pixelbreaker/buteo/buteo-mx/stls/trackpad-lower.stl

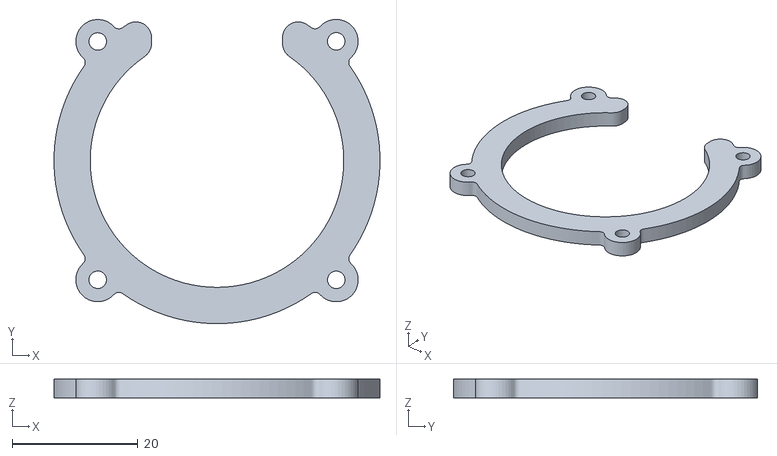
[picture p15: CAD file, 2024-01-28]
buteo-mx/stls/trackpad-lower.stl
51.9 x 48.5 x 3.00
