pixelbreaker/buteo/buteo-mx-azoteq/stls/plate-right.stl

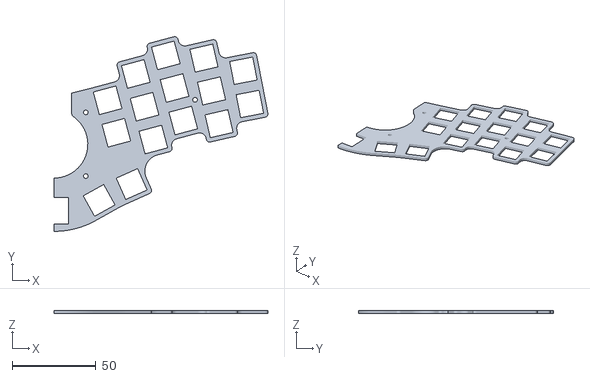
[picture p16: CAD file, 2023-10-03]
buteo-mx-azoteq/stls/plate-right.stl
127.9 x 116.4 x 2.00
